JamesB0T/Windsensor_WiFi_1000/Documentation/German/Windsensor_Bauteilliste.pdf

Tabelle1
Bauteilliste zum Windsensor WiFi 1000
(C) Norbert Walter 2018
Position | Menge | Bauteil | Material

Dokumentation
1 | 1 | Technische Beschreibung
2 | 1 | Zusammenbauanleitung
3 | 1 | Inbetriebnahmeanleitung
4 | 1 | Schaltplan Platine
5 | 1 | Schaltplan Verdrahtung
6 | 1 | Stückliste
7 | 1 | CD mit Software und Doku

3D-Teile
8 | 3 | Schale | PLA
9 | 1 | Frame | PLA
10 | 1 | Rotor | PLA
11 | 1 | Rotor-Fahne | PLA
12 | 1 | Fahnenhalter | PLA
13 | 1 | Fahne | PLA
14 | 1 | Magnethalter | PLA

Mechanikteile
15 | 1 | Spitze | V4A
16 | 1 | Stator | Alu
17 | 1 | Blende | Weissblech
18 | 1 | Befestigungsfuß | Alu
19 | 1 | U-Scheibe M10 | V4A
20 | 1 | Schnorrscheibe M10 | V4A
21 | 1 | Mutter M10 | V4A
22 | 2 | Kugellager 608ZZ | V4A
23 | 1 | Alurohr D10mm, 300 mm | Alu
24 | 1 | Gewindestange M3x80 | V4A
25 | 2 | Inbusschraube M3x8 | V4A
26 | 1 | Inbusschraube M3x10 | V4A
27 | 1 | U-Scheibe M3 | V4A
28 | 2 | Schnorrscheibe M3 | V4A
29 | 2 | Mutter M3 | V4A
30 | 3 | Madenschraube M3x4 | V4A
31 | 1 | U-Scheibe M6 | Nylon
32 | 1 | Magnet D3x6 | Neodym
33 | 1 | Magnet D3x3 | Neodym
34 | 1 | Reflexfolie rot 200 x 50 mm | PVC
35 | 1 | Reflexfolie weiß 50 x 20 mm | PVC

Elektronik
36 | 1 | Platine bestückt mit Software | FR4 1mm
37 | 1 | 8pol. Kabel D 5 x 800 mm | CAT5e
38 | 2 | DC/DC-Wandler

Tabelle1
Hilfsmittel
39 | 1 | Brennspiritus
40 | 1 | Silikonöl / Feinöl
41 | 1 | Klarlack f. Kunststoff Dupli Color
42 | 1 | 2K-Kleber Weicon RK-1300
43 | 1 | Tesafilm
44 | 4 | Q-Tip Ohrstäbchen
45 | 1 | Kabelbinder 4...6 mm Breite
46 | 1 | 9V Blockbatterie
47 | 1 | Schraubensicherungslack | optional

Werkzeug
48 | 1 | Pinzette
49 | 1 | Cuttermesser / Skalpell
50 | 1 | Inbus f. M3
51 | 1 | Inbus f. M2
52 | 1 | Maulschlüssel 5,5er
53 | 1 | Maulschlüssel 17er
54 | 1 | Maulschlüssel 22er
55 | 1 | Feinzange
56 | 1 | Elektronik-Seitenschneider
57 | 1 | Elektronik-Lötkolben
58 | 1 | Lötzinn
59 | 1 | Schraubendreher klein
60 | 1 | Digital-Multimeter
61 | 1 | Entlötlitze | optional
62 | 1 | Osziloskop | optional

Software
63 | 1 | Firmware Windsensor | optional
64 | 1 | Arduino IDE V1.8.5 | optional
65 | 1 | Laptop/PC | optional
66 | 1 | USB/Seriell-Wandler 3,3V | optional
67 | 1 | USB-Kabel | optional
