JamesB0T/Windsensor_WiFi_1000/Android-App/Screenshot_Windsensor_App.png

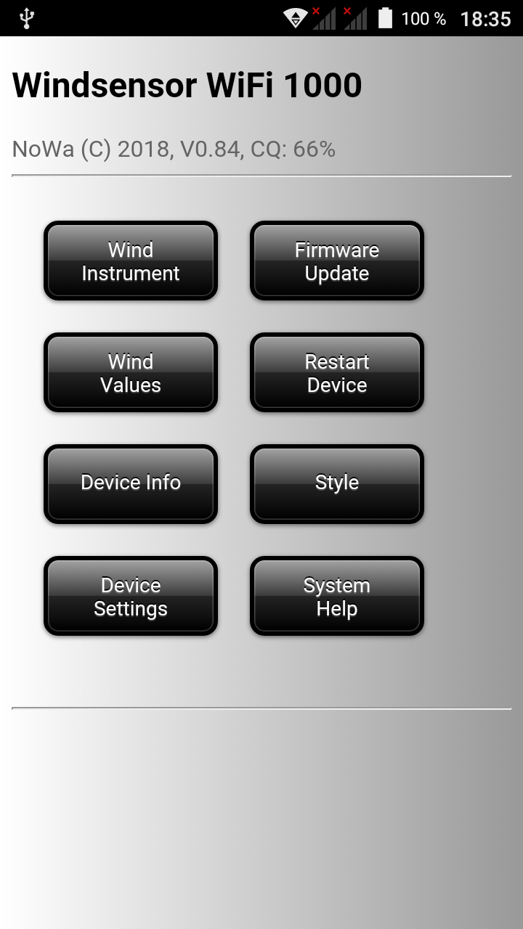
Android-App/Screenshot_Windsensor_App.png
