JamesB0T/Windsensor_WiFi_1000/Android-App/Winsensor_App_Inventor_Blocks.png

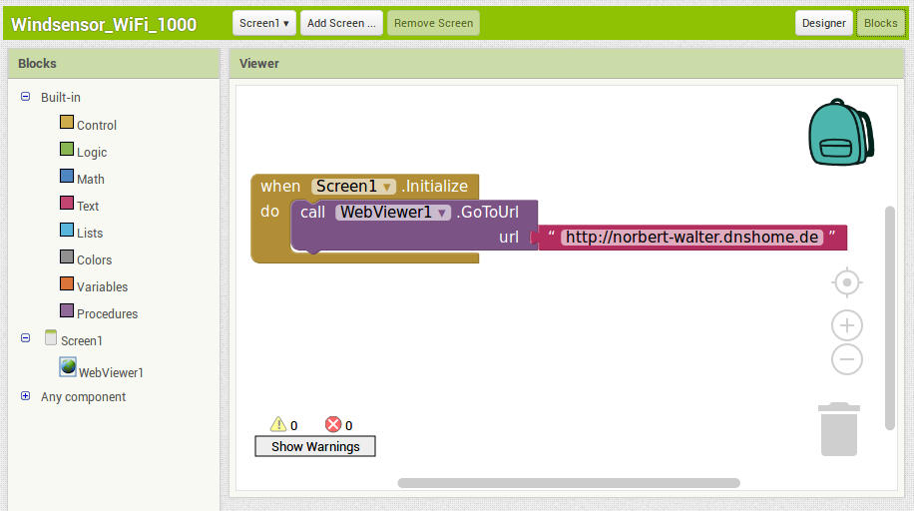
Android-App/Winsensor_App_Inventor_Blocks.png
