JamesB0T/Windsensor_WiFi_1000/Data Sheets/Esp8266_esp_12e_schematics.jpg

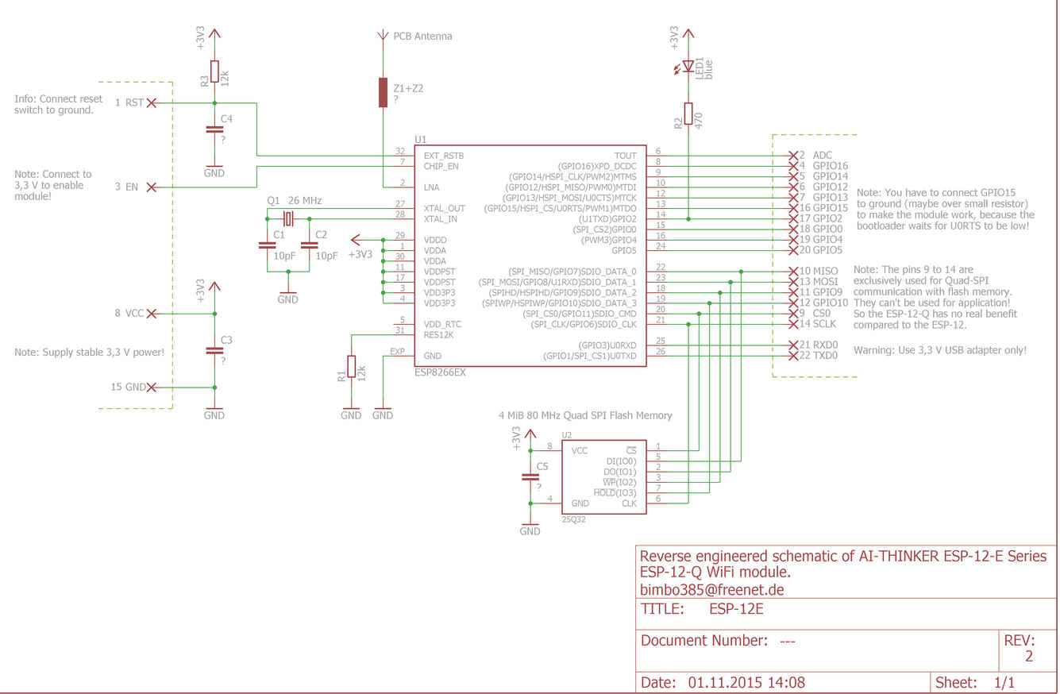
Data Sheets/Esp8266_esp_12e_schematics.jpg
