JamesB0T/Windsensor_WiFi_1000/Pictures/AppConfiguration/Main.png

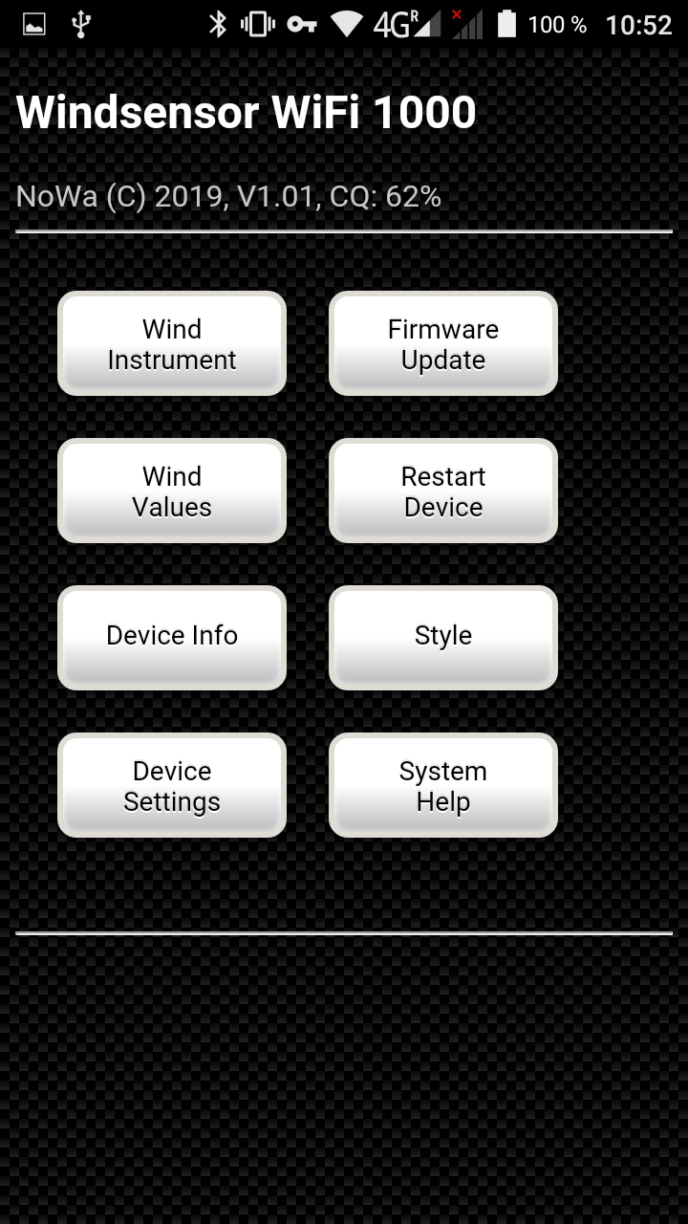
Pictures/AppConfiguration/Main.png
