JamesB0T/Windsensor_WiFi_1000/Pictures/AppConfiguration/Settings1.png

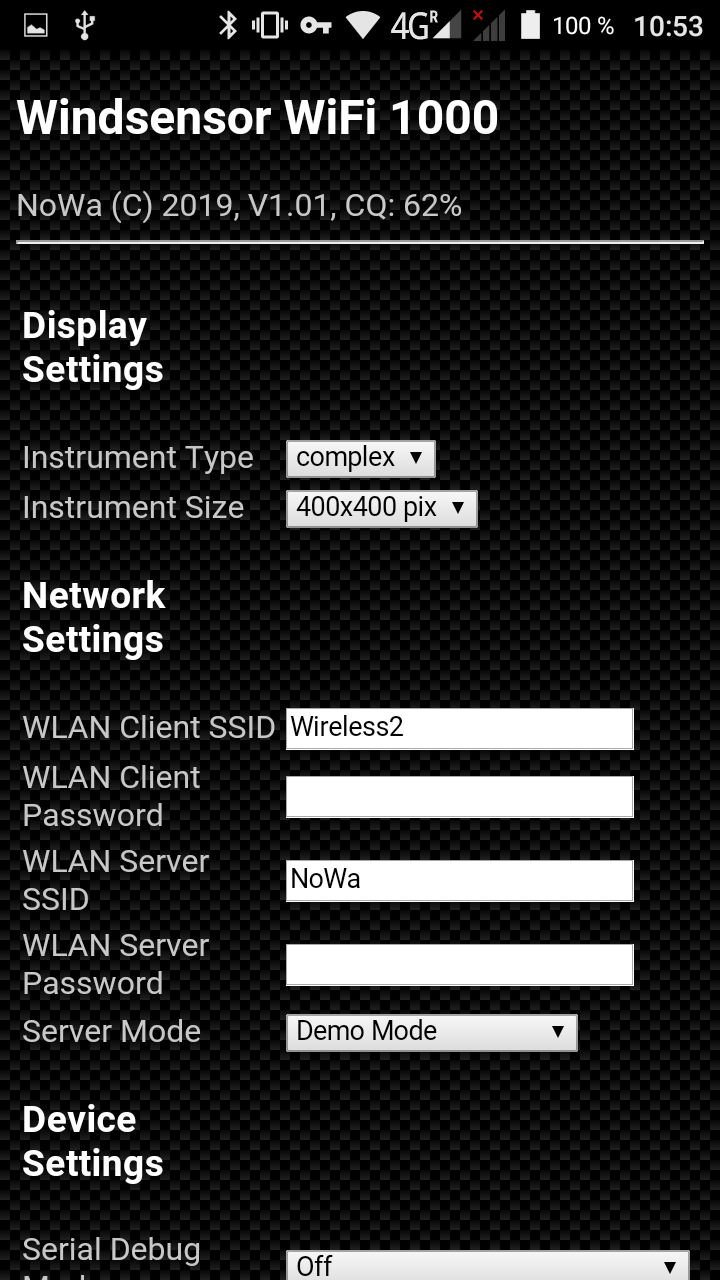
Pictures/AppConfiguration/Settings1.png
