JamesB0T/Windsensor_WiFi_1000/Pictures/ExplodeViews/Windsensor_Bottomparts_Explode.png

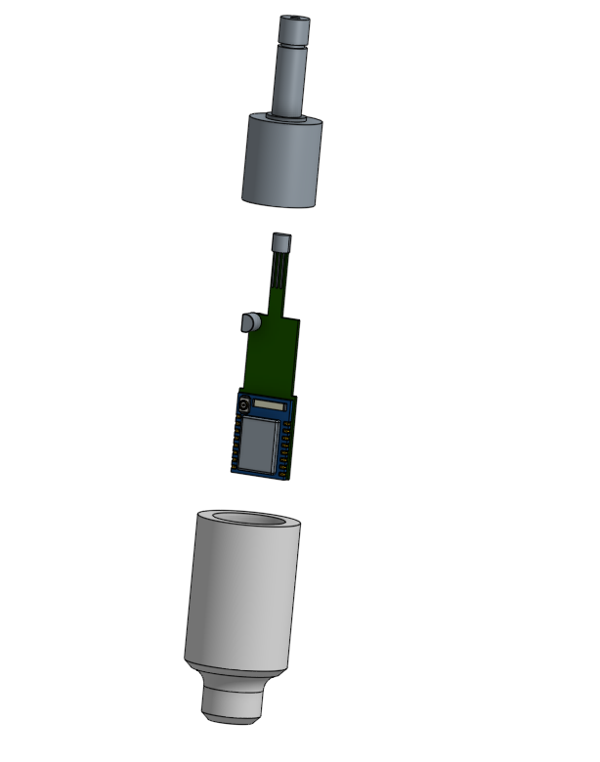
Pictures/ExplodeViews/Windsensor_Bottomparts_Explode.png
