JamesB0T/Windsensor_WiFi_1000/Pictures/ExplodeViews/Windsensor_Explode_alle_Teile_2.png

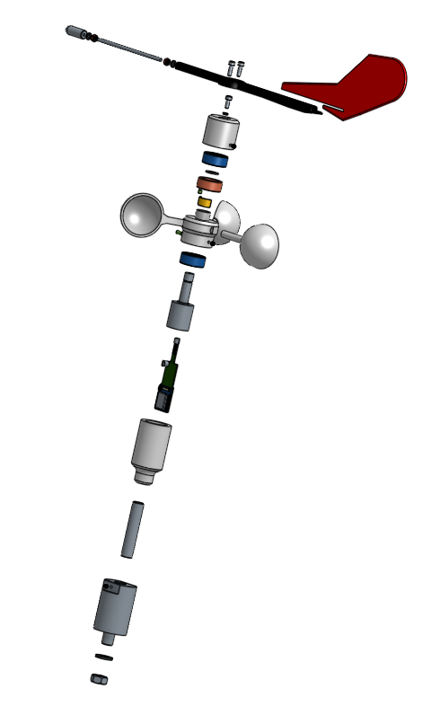
Pictures/ExplodeViews/Windsensor_Explode_alle_Teile_2.png
