JamesB0T/Windsensor_WiFi_1000/Pictures/ExplodeViews/Windsensor_Topparts_Explode_2.png

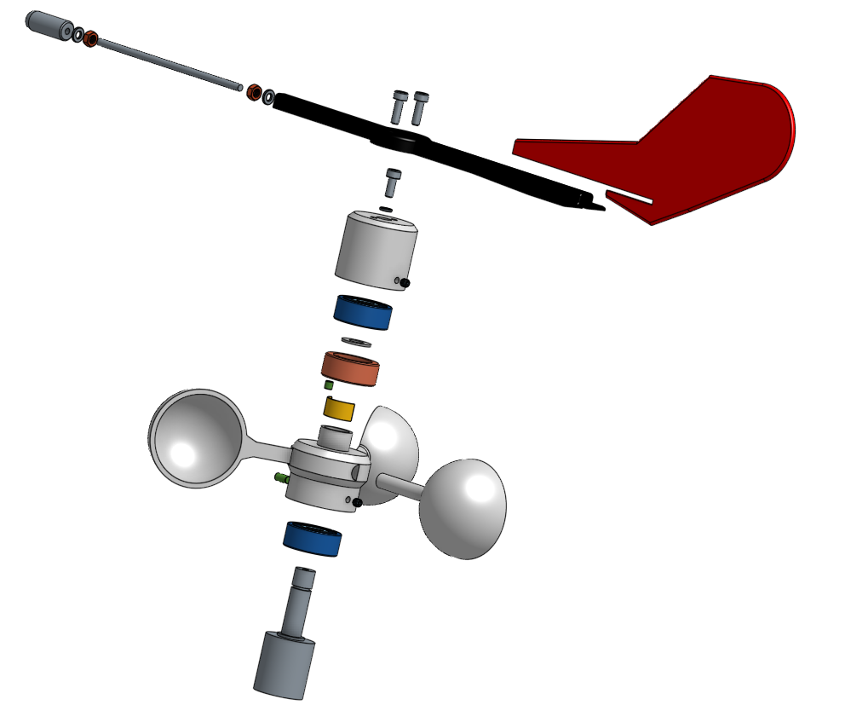
Pictures/ExplodeViews/Windsensor_Topparts_Explode_2.png
