JamesB0T/Windsensor_WiFi_1000/Pictures/OpenPlotter/OpenPlotter_Device.png

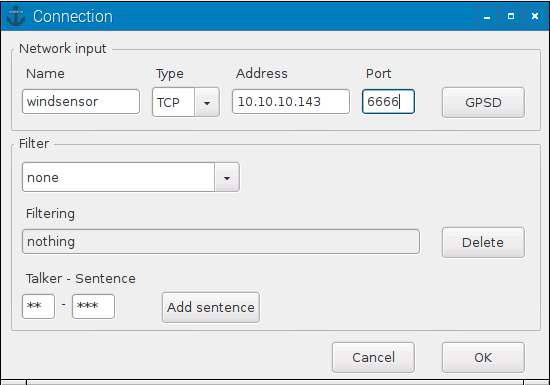
Pictures/OpenPlotter/OpenPlotter_Device.png
