JamesB0T/Windsensor_WiFi_1000/Pictures/OpenPlotter/OpenPlotter_Inspector.png

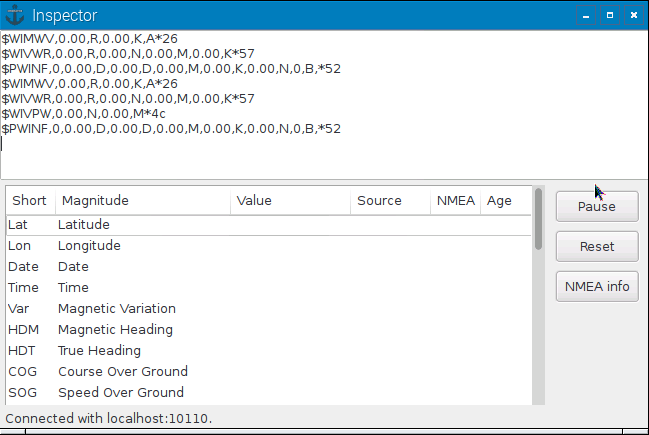
Pictures/OpenPlotter/OpenPlotter_Inspector.png
