JamesB0T/Windsensor_WiFi_1000/Pictures/OpenPlotter/OpenPlotter_NMEA0183.png

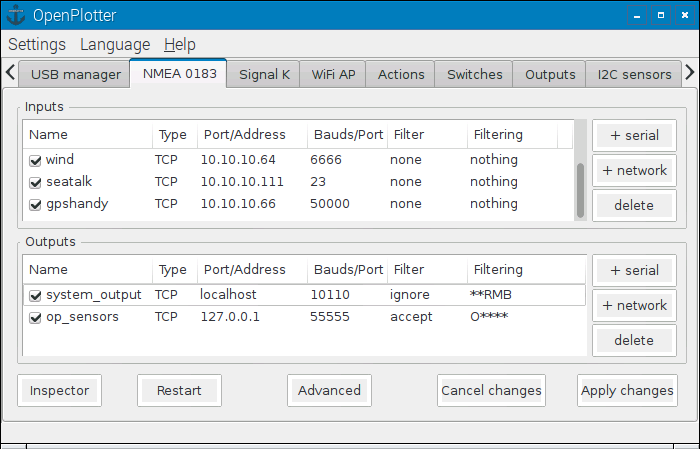
Pictures/OpenPlotter/OpenPlotter_NMEA0183.png
