JamesB0T/Windsensor_WiFi_1000/Pictures/OpenPlotter/Windsensor_Handy_Tablett.png

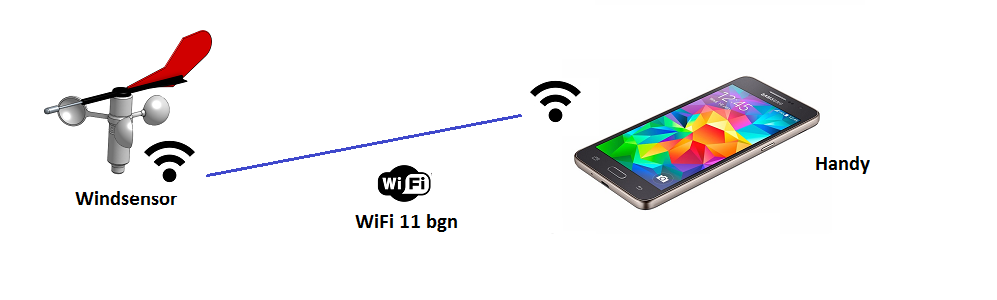
Pictures/OpenPlotter/Windsensor_Handy_Tablett.png
