JamesB0T/Windsensor_WiFi_1000/Pictures/OpenPlotter/Windsensor_Raspi.png

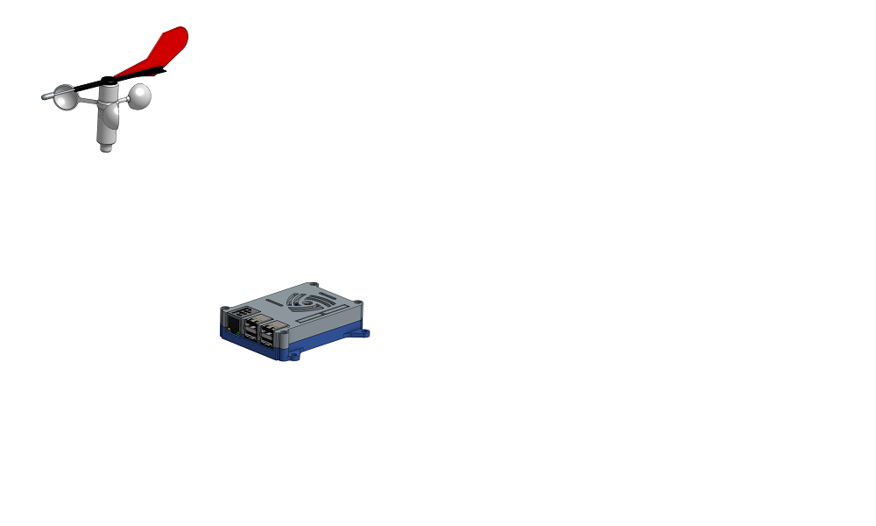
Pictures/OpenPlotter/Windsensor_Raspi.png
