JamesB0T/Windsensor_WiFi_1000/Pictures/OpenPlotter/Windsensor_Raspi_NMEA2000.png

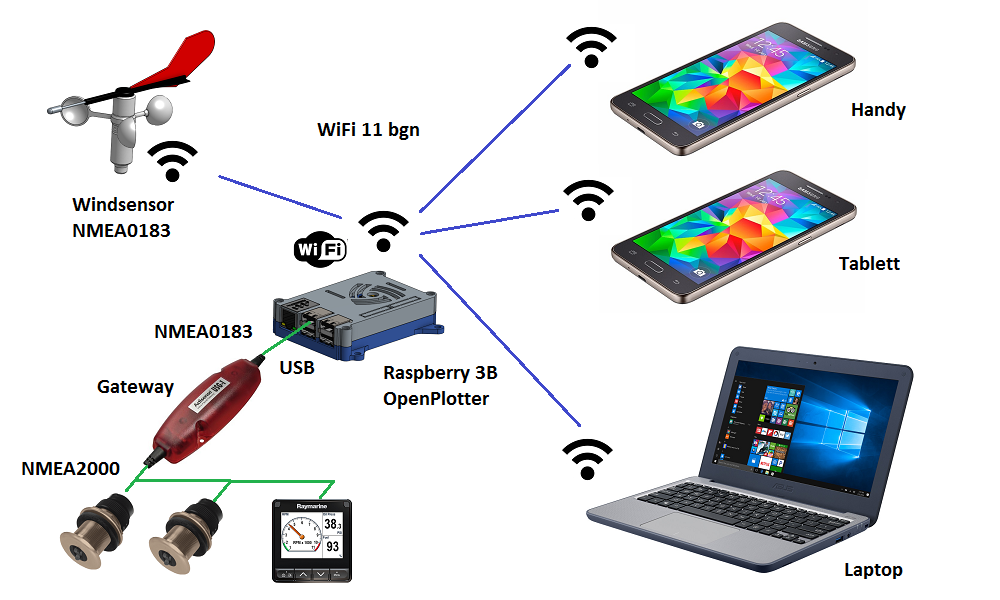
Pictures/OpenPlotter/Windsensor_Raspi_NMEA2000.png
