JamesB0T/Windsensor_WiFi_1000/Pictures/WebConfiguration/Instrument2.png

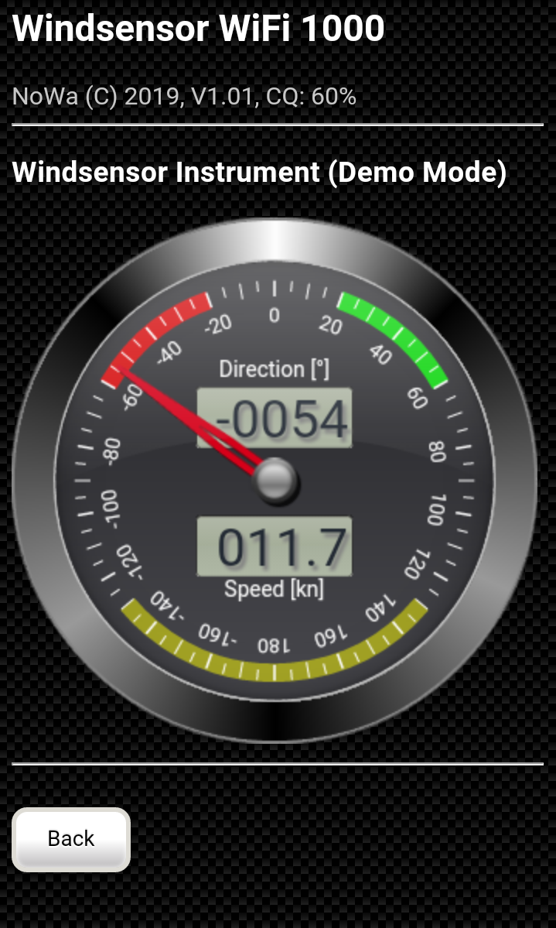
Pictures/WebConfiguration/Instrument2.png
