JamesB0T/Windsensor_WiFi_1000/Pictures/Windsensor3.png

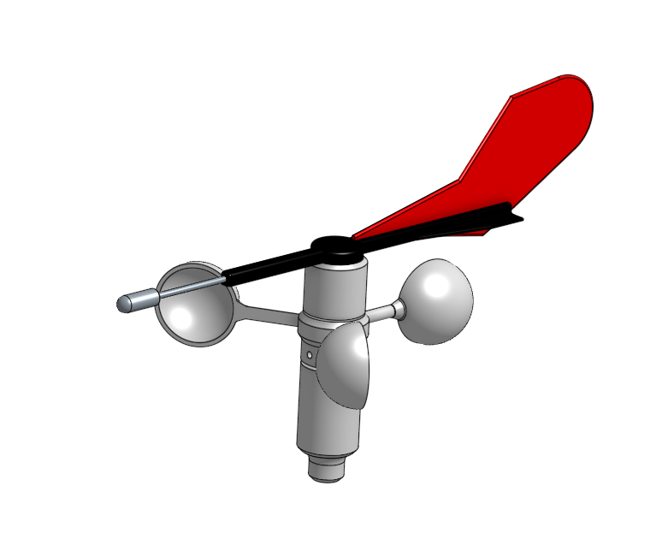
Pictures/Windsensor3.png
