JamesB0T/Windsensor_WiFi_1000/Simulation-Files/Magnetical Simulation/Animated_Simulation_120_grd.gif

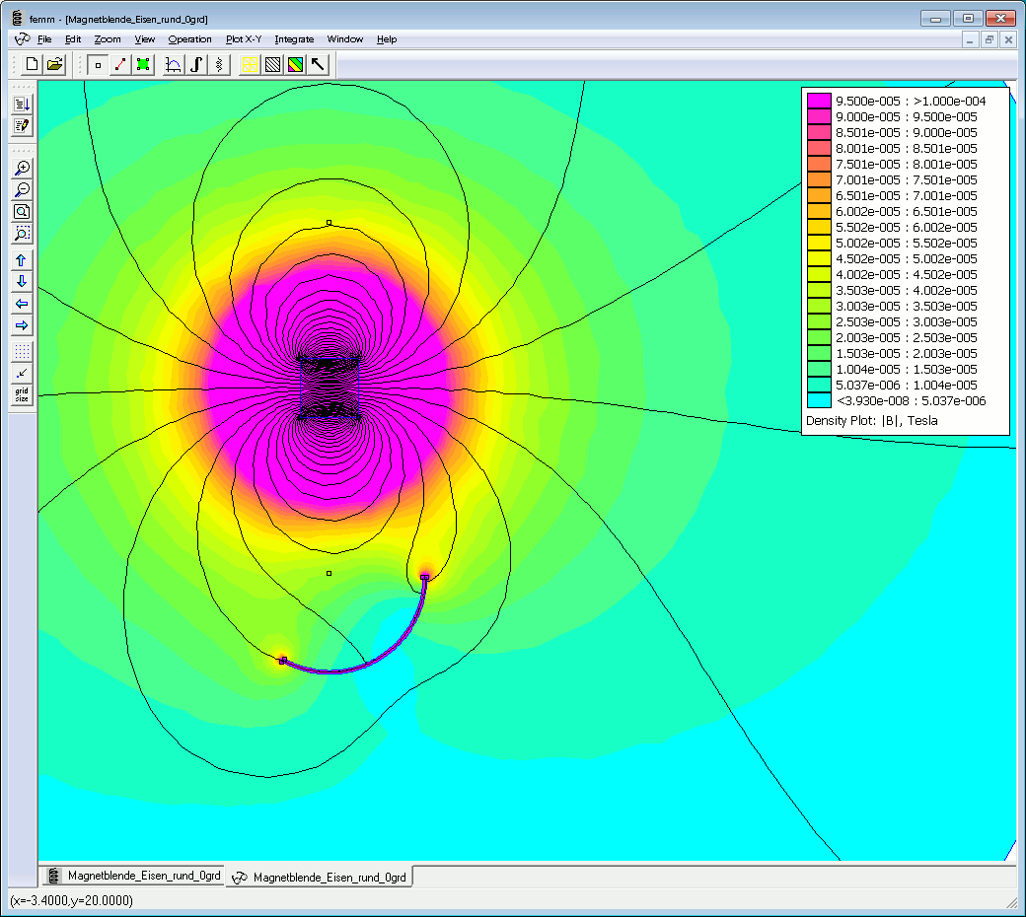
Simulation-Files/Magnetical Simulation/Animated_Simulation_120_grd.gif
