JamesB0T/Windsensor_WiFi_1000/Simulation-Files/Magnetical Simulation/Animated_Simulation_180_grd.gif

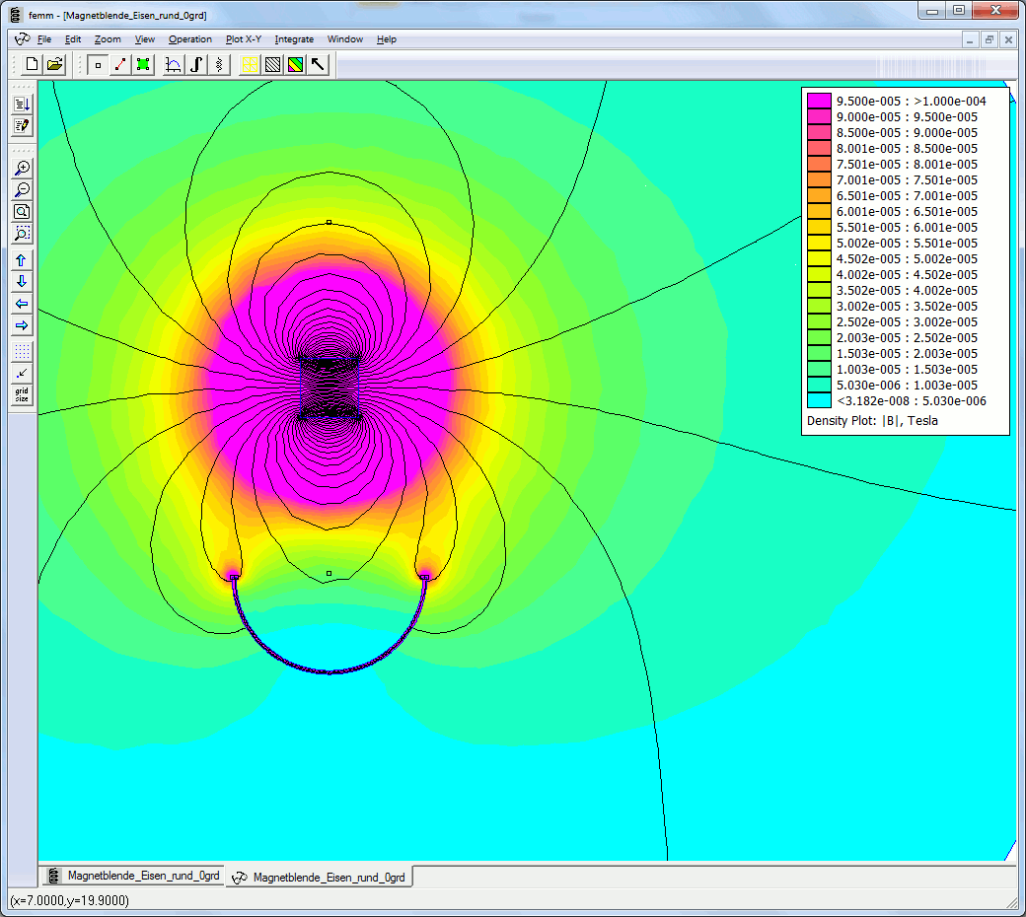
Simulation-Files/Magnetical Simulation/Animated_Simulation_180_grd.gif
