JamesB0T/Windsensor_WiFi_1000/Simulation-Files/Magnetical Simulation/Eisen_0.3mm_-1mm.png

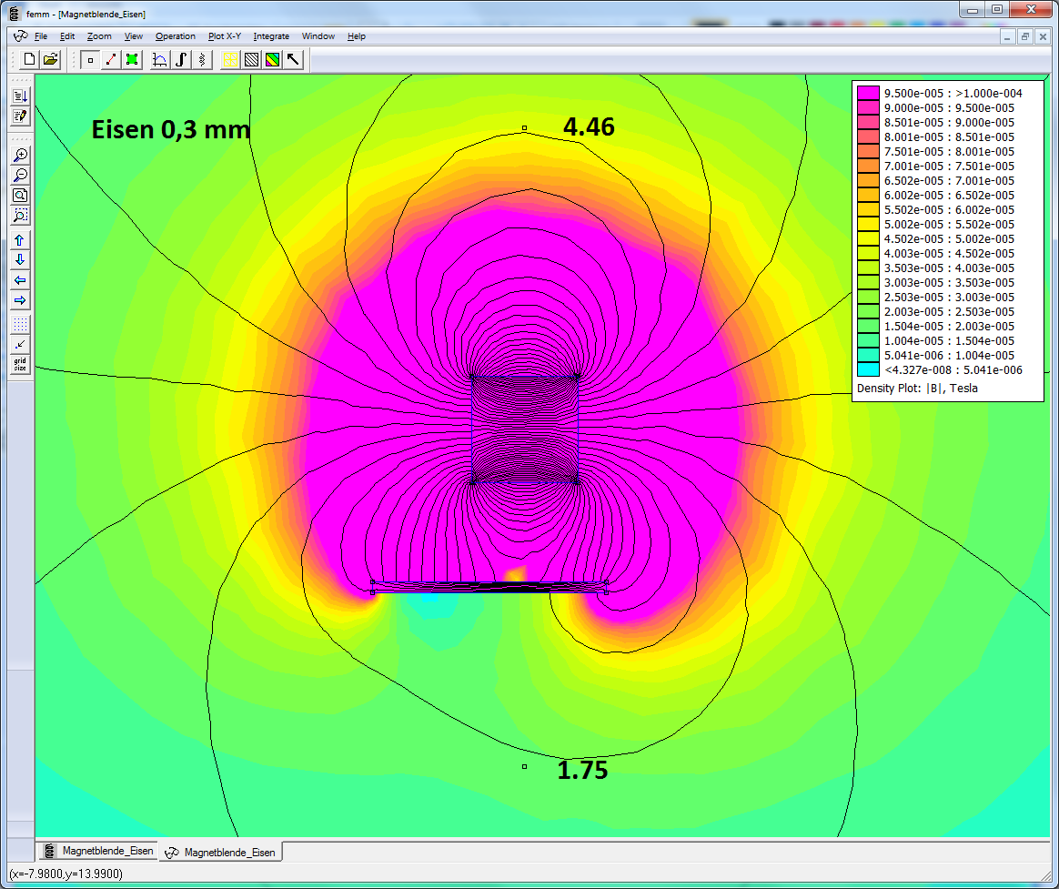
Simulation-Files/Magnetical Simulation/Eisen_0.3mm_-1mm.png
