JamesB0T/Windsensor_WiFi_1000/Simulation-Files/Magnetical Simulation/Feldstärkeverlauf_alle.png

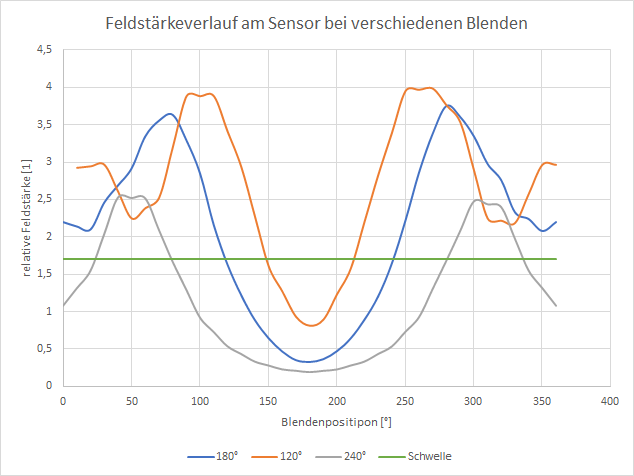
Simulation-Files/Magnetical Simulation/Feldstärkeverlauf_alle.png
