JamesB0T/Windsensor_WiFi_1000/Simulation-Files/Magnetical Simulation/Mumetall_0.3mm.png

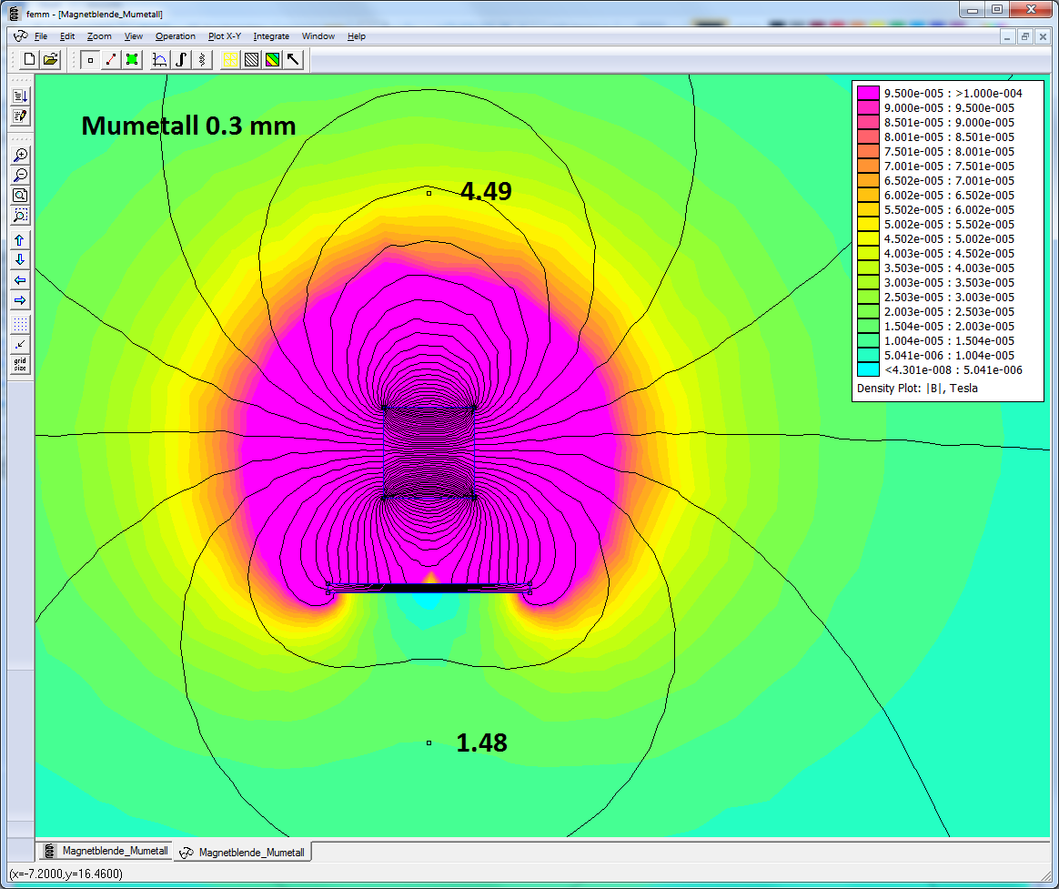
Simulation-Files/Magnetical Simulation/Mumetall_0.3mm.png
