JamesB0T/Windsensor_WiFi_1000/Simulation-Files/Magnetical Simulation/Sensor_Schaltschwelle.png

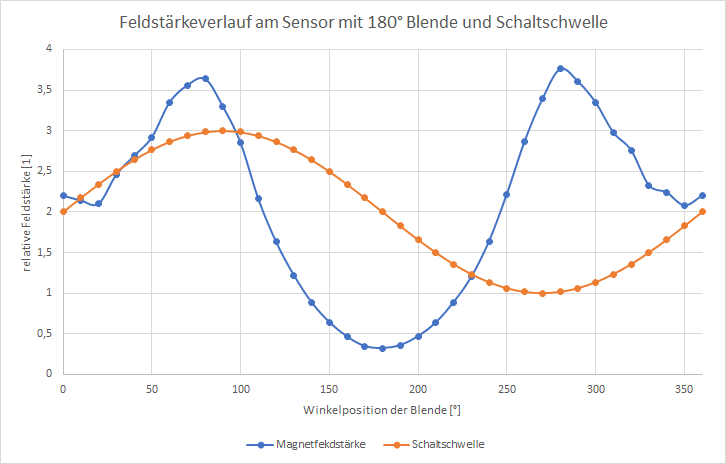
Simulation-Files/Magnetical Simulation/Sensor_Schaltschwelle.png
