JamesB0T/Windsensor_WiFi_1000/Simulation-Files/Mechanical Simulation/BlocksCAD3D.png

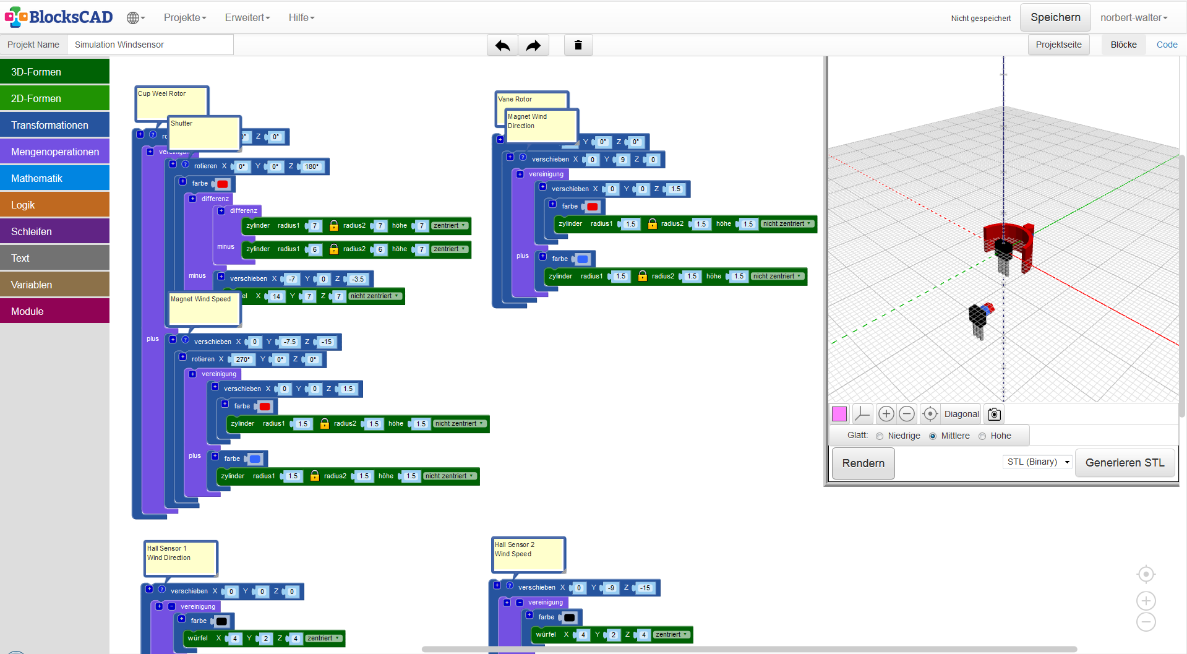
Simulation-Files/Mechanical Simulation/BlocksCAD3D.png
