JamesB0T/Windsensor_WiFi_1000/Pictures/Assembly3D/Blende2.png

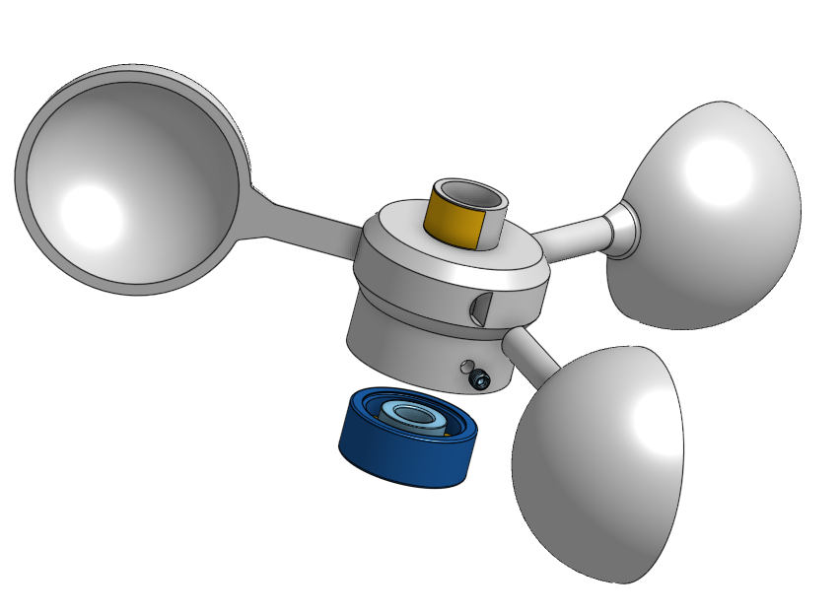
Pictures/Assembly3D/Blende2.png
