JamesB0T/Windsensor_WiFi_1000/Pictures/Assembly3D/Frame_mit_Platine_und_Stator.png

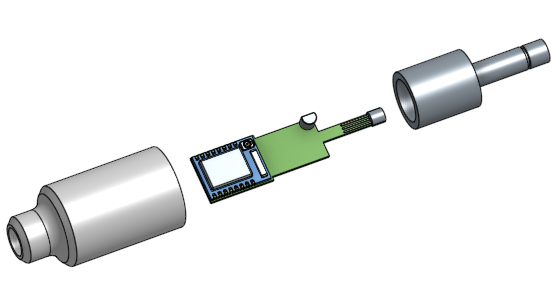
Pictures/Assembly3D/Frame_mit_Platine_und_Stator.png
