JamesB0T/Windsensor_WiFi_1000/Pictures/Assembly3D/Magnet Windfahne 2.png

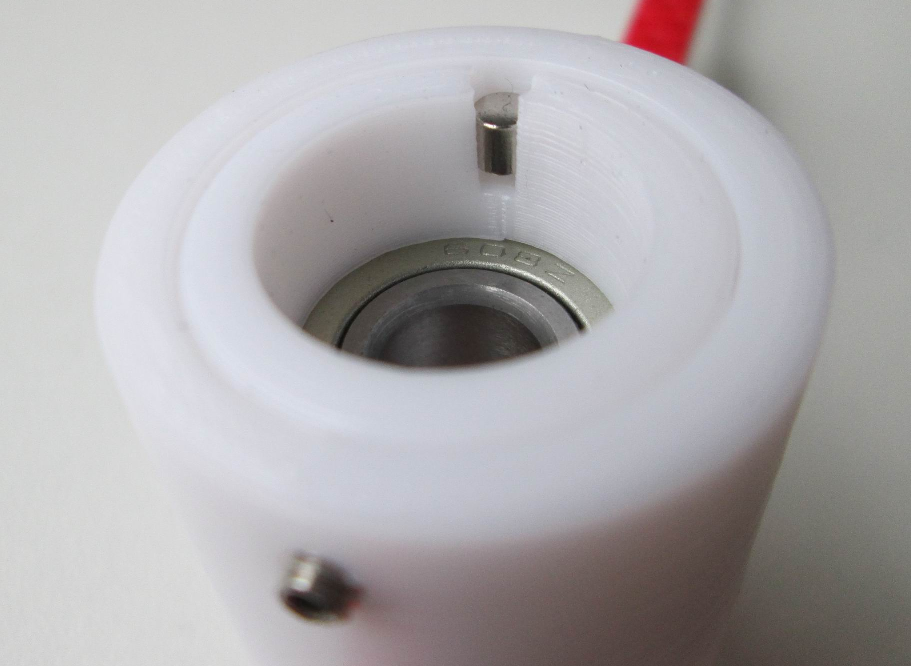
Pictures/Assembly3D/Magnet Windfahne 2.png
