JamesB0T/Windsensor_WiFi_1000/Pictures/Assembly3D/Magnet Windfahne 3.png

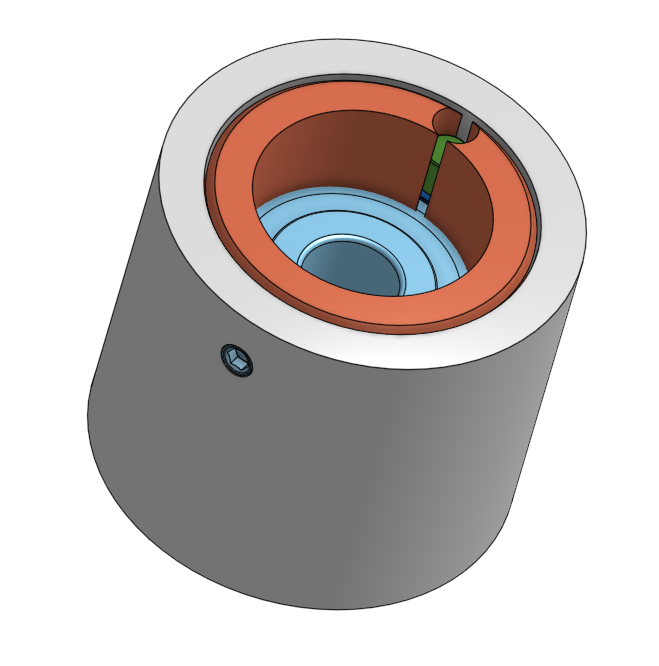
Pictures/Assembly3D/Magnet Windfahne 3.png
