JamesB0T/Windsensor_WiFi_1000/Pictures/AssemblyReal/GrößenänderungIMG_3774.JPG

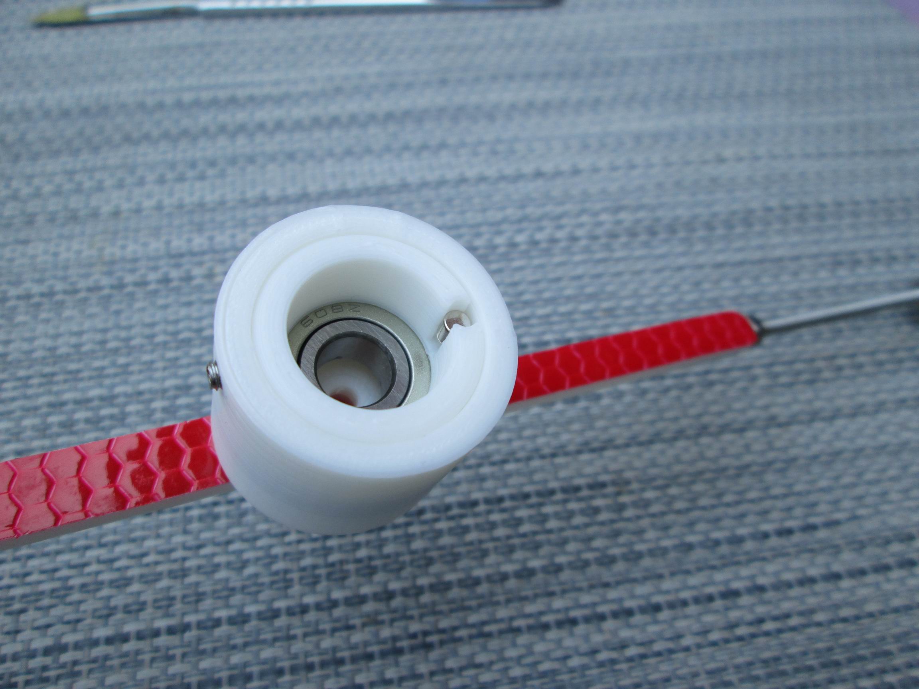
Pictures/AssemblyReal/GrößenänderungIMG_3774.JPG
