JamesB0T/Windsensor_WiFi_1000/Pictures/AssemblyReal/GrößenänderungIMG_3776.JPG

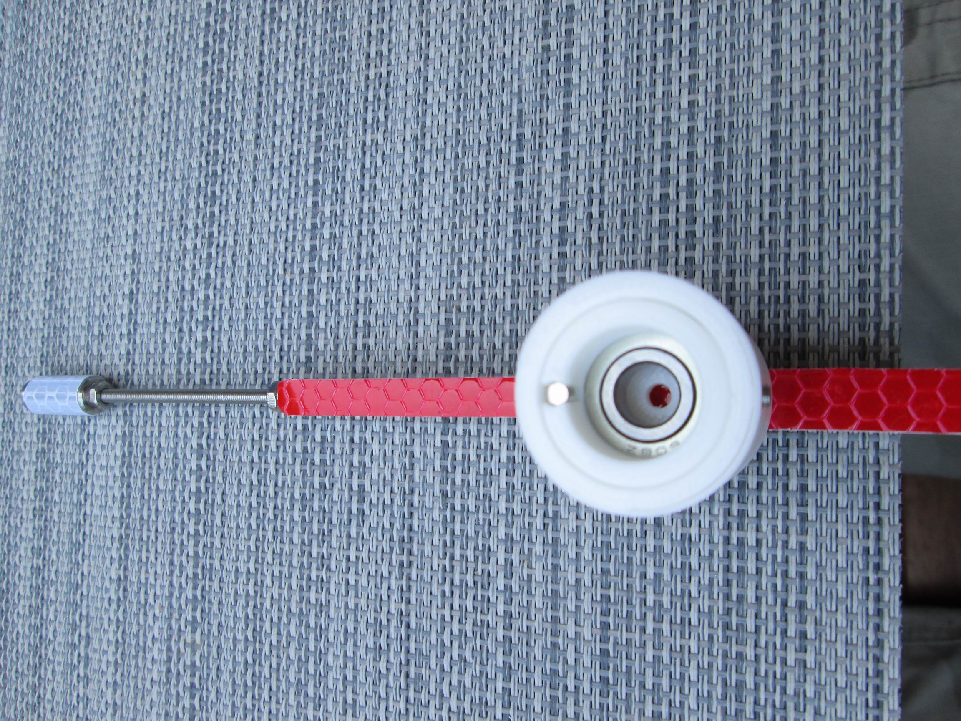
Pictures/AssemblyReal/GrößenänderungIMG_3776.JPG
