JamesB0T/Windsensor_WiFi_1000/Pictures/AssemblyReal/GrößenänderungIMG_3777.JPG

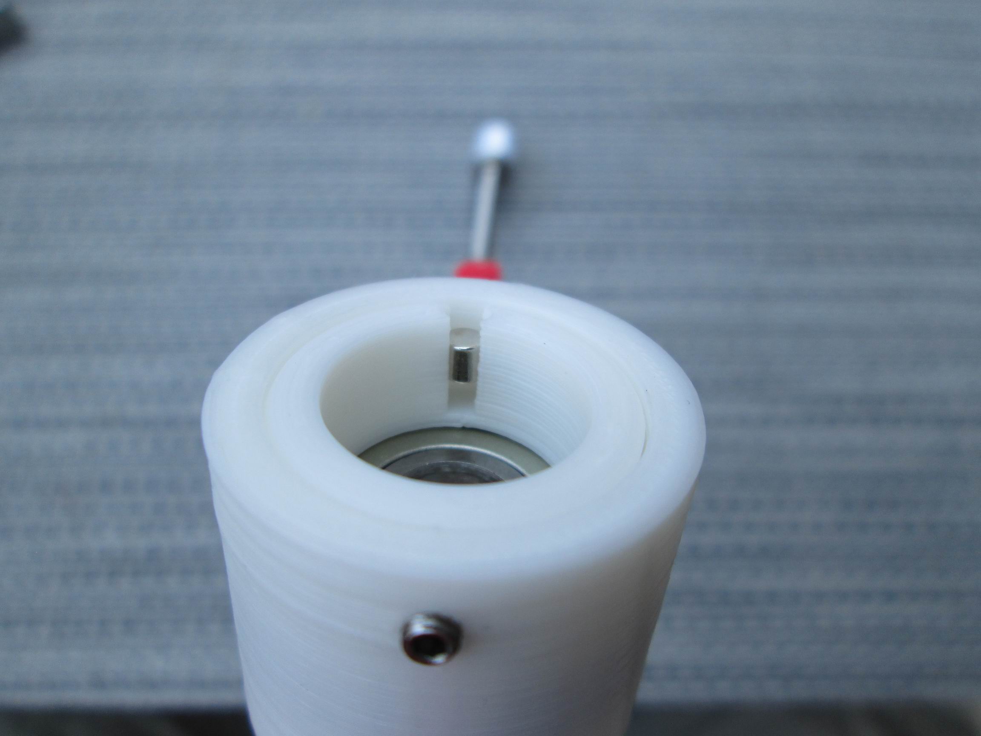
Pictures/AssemblyReal/GrößenänderungIMG_3777.JPG
