JamesB0T/Windsensor_WiFi_1000/Pictures/AssemblyReal/GrößenänderungIMG_3800.JPG

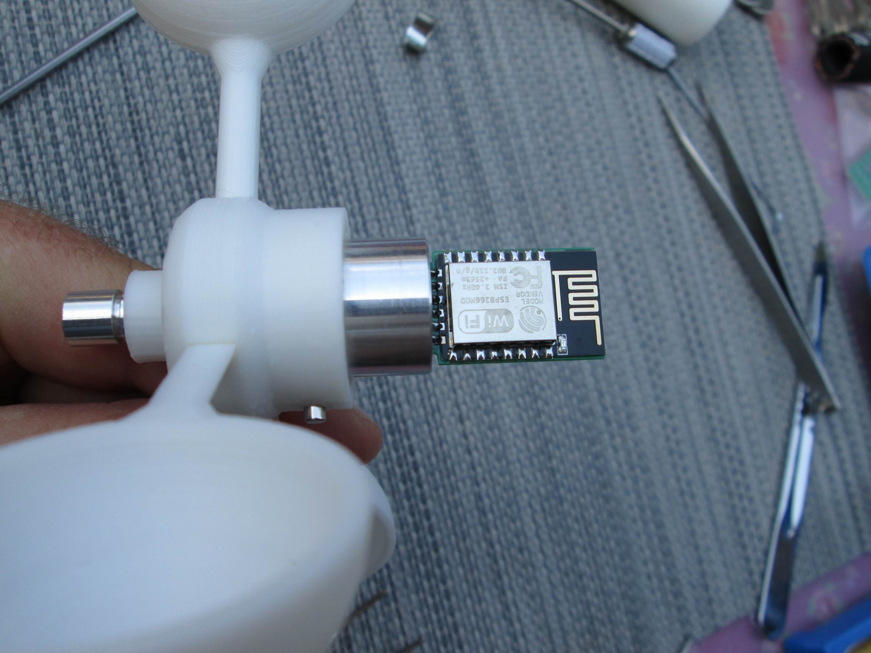
Pictures/AssemblyReal/GrößenänderungIMG_3800.JPG
