JamesB0T/Windsensor_WiFi_1000/Pictures/AssemblyReal/GrößenänderungIMG_3809.JPG

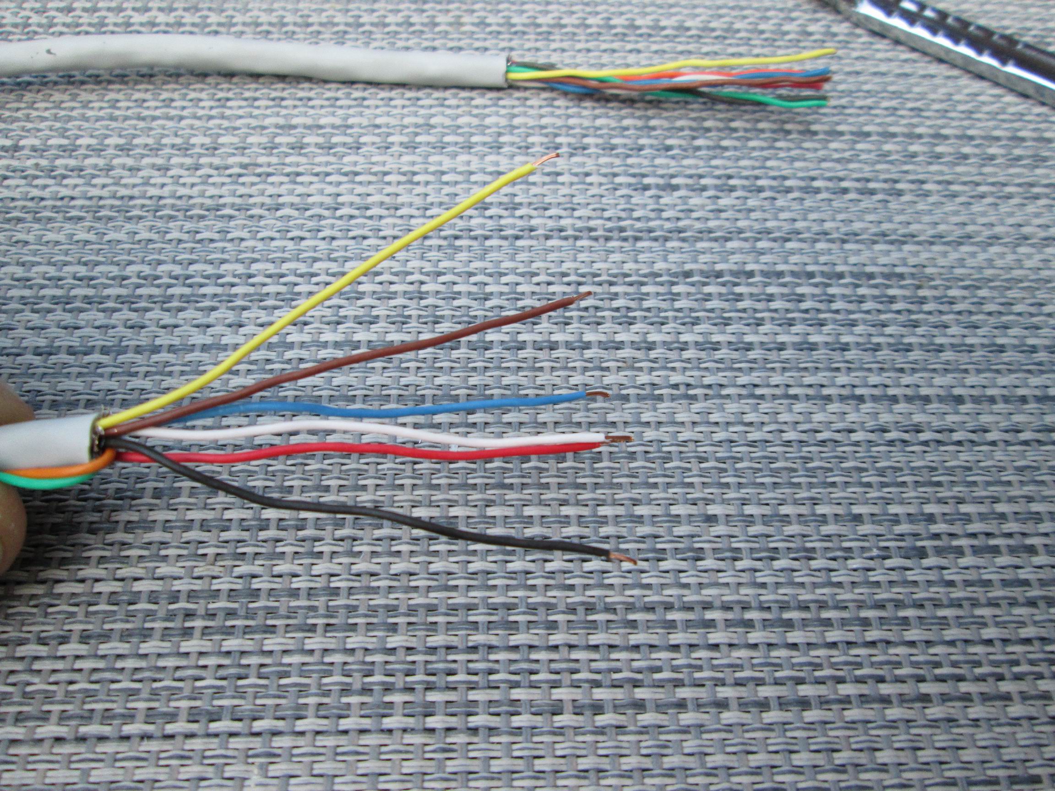
Pictures/AssemblyReal/GrößenänderungIMG_3809.JPG
