JamesB0T/Windsensor_WiFi_1000/CAD-Files/Eagle/Windsensor5.pdf

A

A

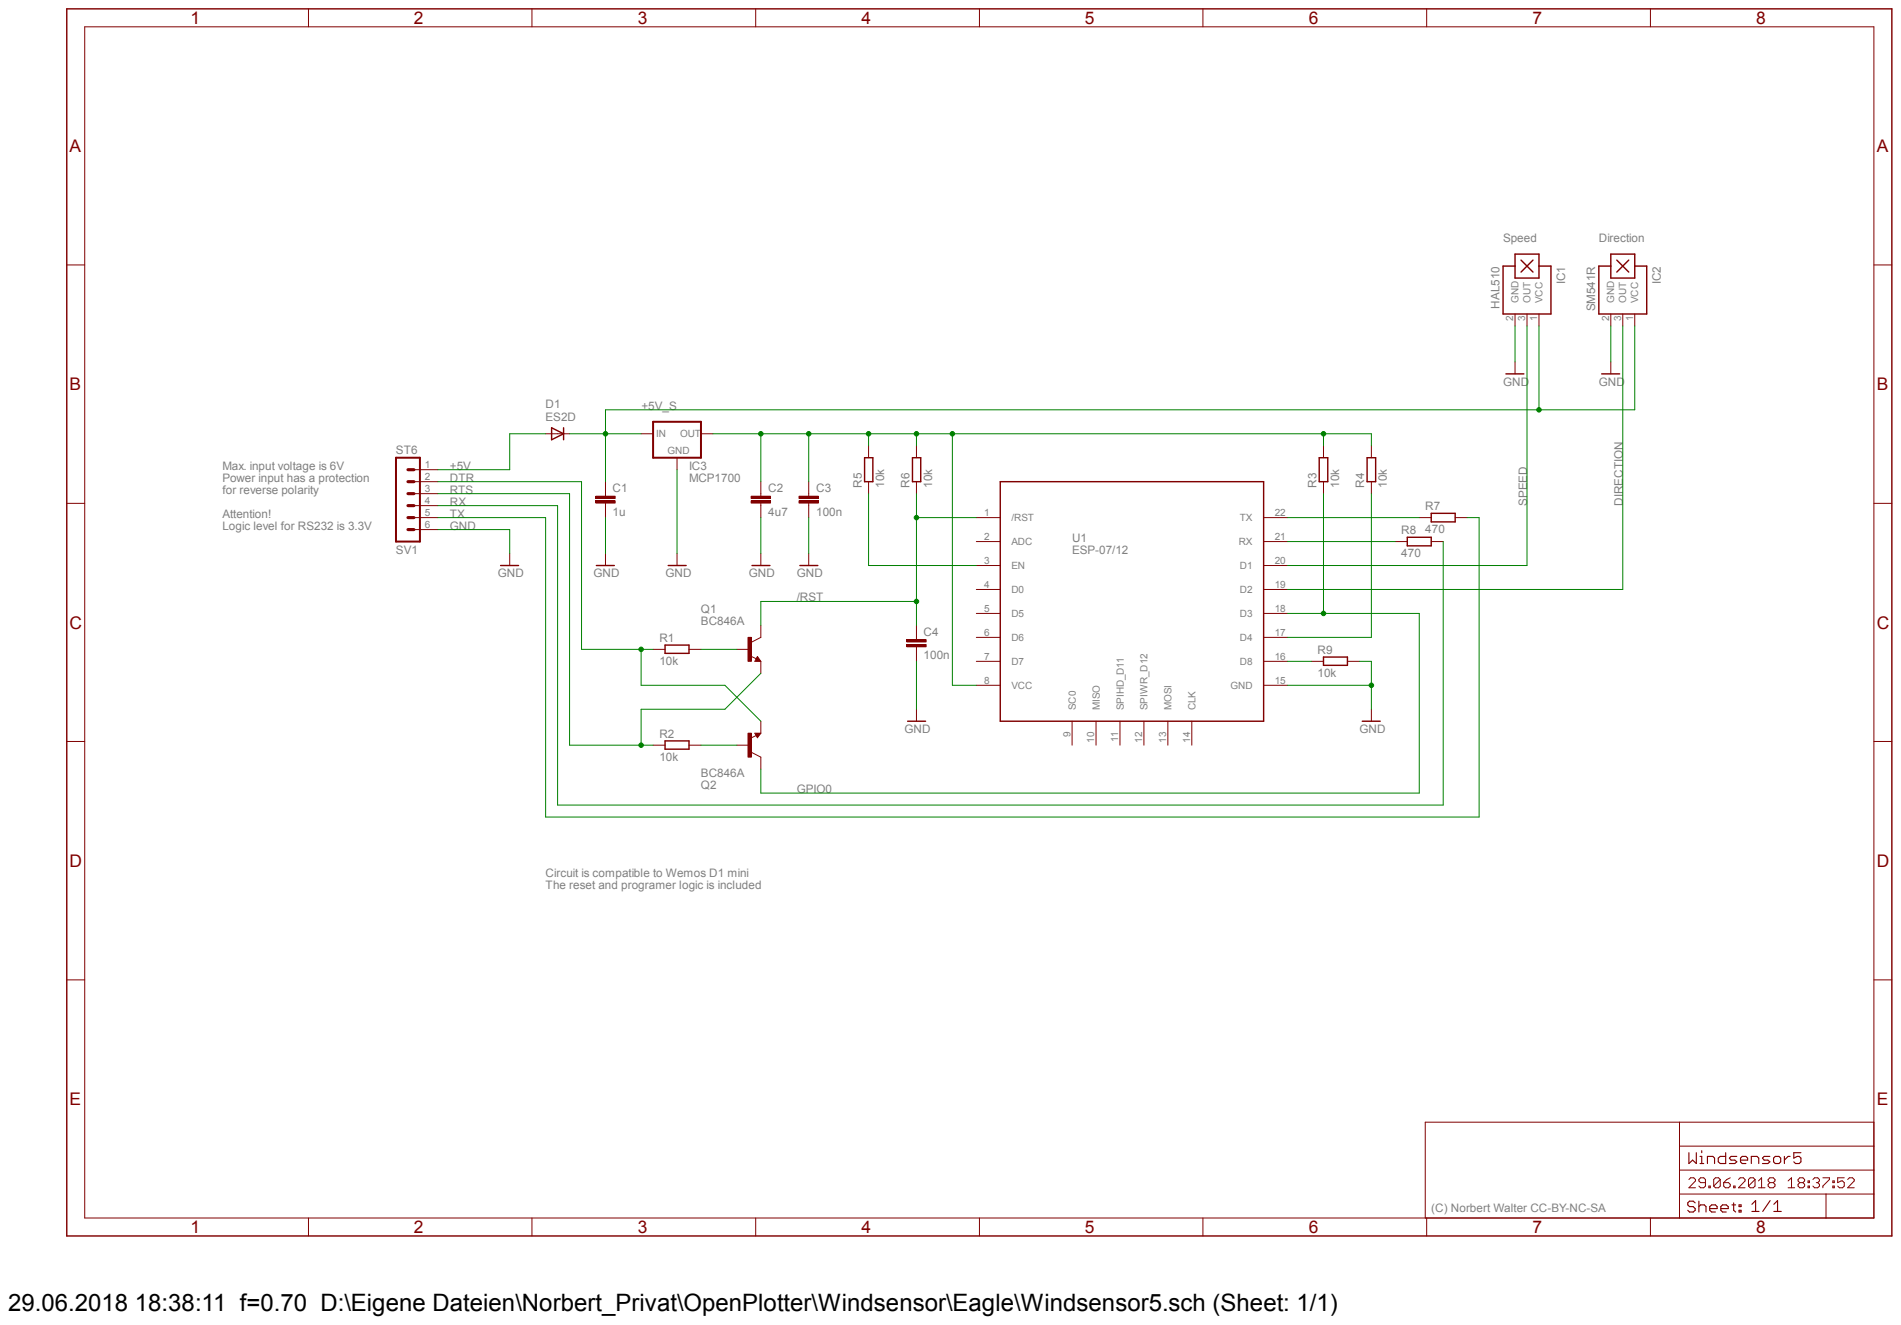
[picture p204: page 1]

Max. input voltage is 6V
Power input has a protection
for reverse polarity

Attention!
Logic level for RS232 is 3.3V

Circuit is compatible to Wemos D1 mini
The reset and programer logic is included

(C) Norbert Walter CC-BY-NC-SA

29.06.2018 18:38:11 f=0.70 D:\Eigene Dateien\Norbert_Privat\OpenPlotter\Windsensor\Eagle\Windsensor5.sch (Sheet: 1/1)
