JamesB0T/Windsensor_WiFi_1000/CAD-Files/Eagle/Schaltplan.pdf

A

A

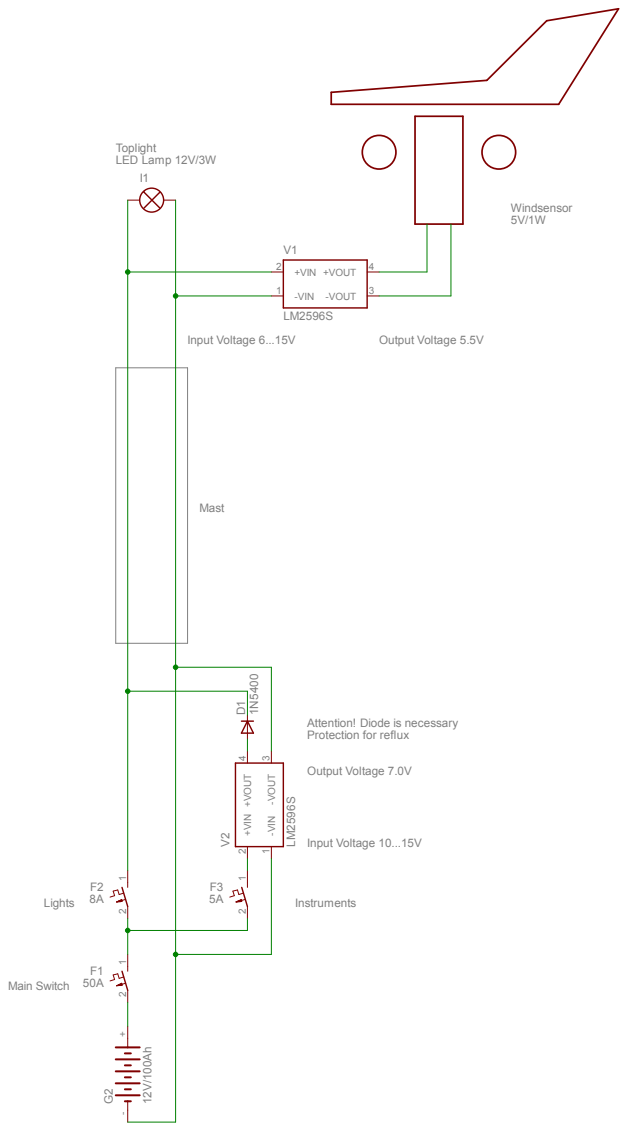
[picture p205: page 1]
LED Lamp 12V/3W; Output Voltage 5.5V; Output Voltage 7.0V; Input Voltage 10...15V; Input Voltage 6...15V; Toplight; Windsensor; Lights; Instruments; Main Switch; Mast; +VIN 2; -VIN 1; +VOUT; -VOUT; +VIN; -VIN

Attention! Diode is necessary
Protection for reflux

(C) Norbert Walter CC-BY-NC-SA

29.06.2018 18:35:53 f=0.70 D:\Eigene Dateien\Norbert_Privat\OpenPlotter\Windsensor\Eagle\Schaltplan.sch (Sheet: 1/1)
