JamesB0T/Windsensor_WiFi_1000/CAD-Files/Eagle/BS_Windsensor5.pdf

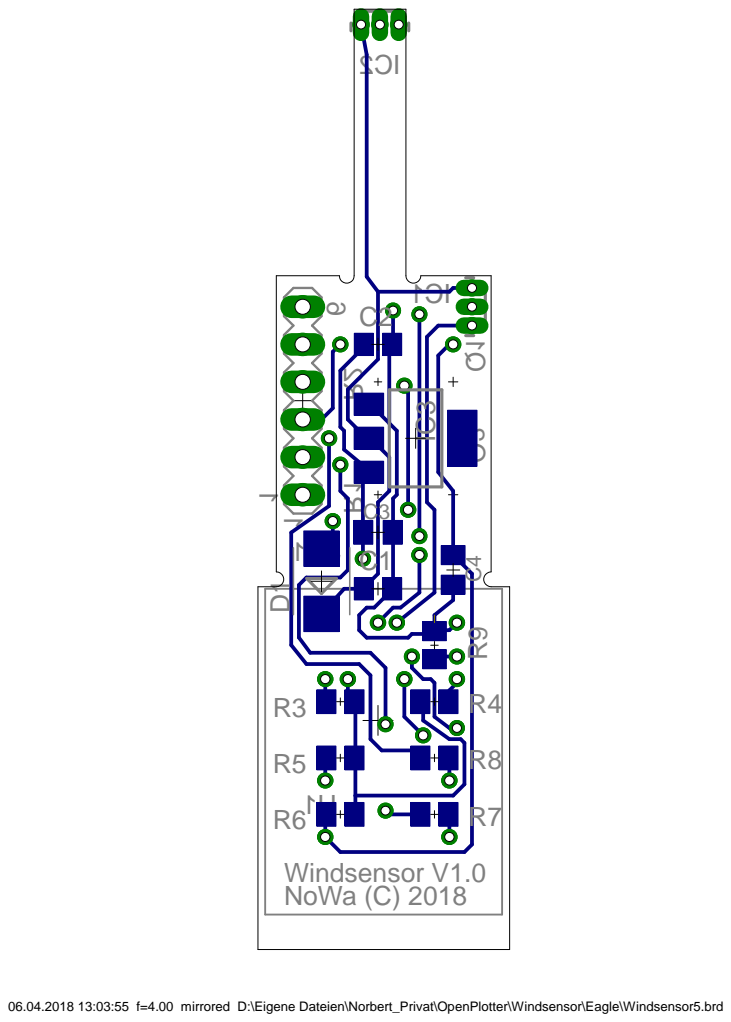
[picture p209: page 1]

06.04.2018 13:03:55 f=4.00 mirrored D:\Eigene Dateien\Norbert_Privat\OpenPlotter\Windsensor\Eagle\Windsensor5.brd
