JamesB0T/Windsensor_WiFi_1000/CAD-Files/Eagle/TS_Windsensor5.pdf

IC2

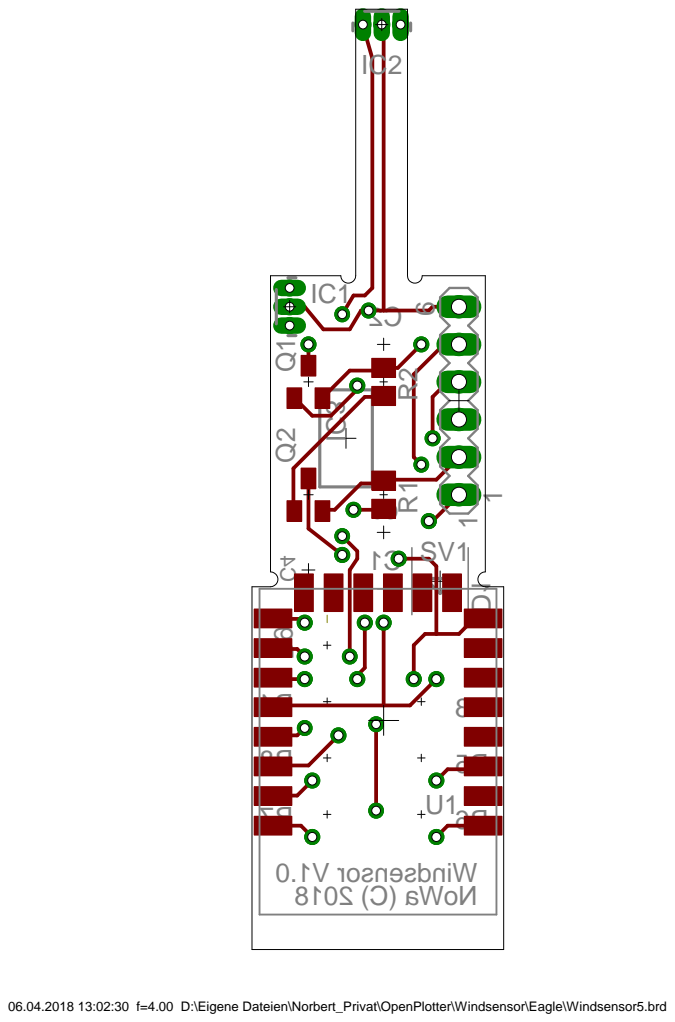
[picture p210: page 1]

06.04.2018 13:02:30 f=4.00 D:\Eigene Dateien\Norbert_Privat\OpenPlotter\Windsensor\Eagle\Windsensor5.brd
